wszeto9/ESP32-S3-HUB75-Driver/Firmware/007Gameboard/Gameboard_2025/ImageAssets.h

static char SwitchDisconnectedWhite[] = {
0x00, 0x00, 0x00, 0x00, 0x00, 0x00, 0x00, 0x00, 0x00, 0x00, 0x00, 0x00, 0x00, 0x00, 0x00, 0x00,
0x00, 0x00, 0x00, 0x00, 0x00, 0x00, 0x00, 0x00, 0x00, 0x00, 0x00, 0x00, 0x00, 0x00, 0x00, 0x00,
0x00, 0x0c, 0x00, 0x00, 0x00, 0x1e, 0x00, 0x00, 0xf8, 0xff, 0xff, 0x07, 0xf8, 0xff, 0xff, 0x07,
0xf8, 0xff, 0xff, 0x07, 0xf8, 0xff, 0xff, 0x07, 0xf8, 0xff, 0xff, 0x07, 0xf8, 0xff, 0xff, 0x07,
0xf8, 0xff, 0xff, 0x07, 0xf8, 0xff, 0xff, 0x07, 0xf8, 0xff, 0xff, 0x07, 0xf8, 0xff, 0xff, 0x07,
0x00, 0x00, 0x00, 0x00, 0x00, 0x00, 0x00, 0x00, 0x00, 0x00, 0x00, 0x00, 0x00, 0x00, 0x00, 0x00,
0x00, 0x00, 0x00, 0x00, 0x00, 0x00, 0x00, 0x00, 0x00, 0x00, 0x00, 0x00, 0x00, 0x00, 0x00, 0x00,
0x00, 0x00, 0x00, 0x00, 0x00, 0x00, 0x00, 0x00, 0x00, 0x00, 0x00, 0x00, 0x00, 0x00, 0x00, 0x00,
0x00, 0x00, 0x00, 0x00, 0x00, 0x00, 0x00, 0x00, 0x00, 0x00, 0x00, 0x00, 0x00, 0x00, 0x00, 0x00,
0x00, 0x00, 0x00, 0x00, 0x00, 0x00, 0x00, 0x00, 0x00, 0x00, 0x00, 0x00, 0x00, 0x00, 0x00, 0x00,
0x00, 0x00, 0x00, 0x00, 0x00, 0x00, 0x00, 0x00, 0x00, 0x00, 0x00, 0x00, 0x00, 0x00, 0x00, 0x00,
0x00, 0x00, 0x00, 0x00, 0x00, 0x00, 0x00, 0x00, 0x00, 0x00, 0x00, 0x00, 0x00, 0x00, 0x00, 0x00,
0x00, 0x00, 0x00, 0x00, 0x00, 0x00, 0x00, 0x00, 0x00, 0x00, 0x00, 0x00, 0x00, 0x00, 0x00, 0x00,
0xe0, 0xd2, 0x5d, 0x02, 0x20, 0x52, 0x44, 0x01, 0x20, 0xde, 0xc5, 0x00, 0x20, 0x52, 0x44, 0x01,
0xe0, 0xd2, 0x5d, 0x02, 0x00, 0x00, 0x00, 0x00, 0x9c, 0xa8, 0xef, 0x12, 0x84, 0x28, 0x22, 0x12,
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
0x00, 0x00, 0x00, 0x00, 0x00, 0x00, 0x00, 0x00, 0x00, 0x00, 0x00, 0x00, 0x00, 0x00, 0x00, 0x00,
0x00, 0x00, 0x00, 0x00, 0x00, 0x00, 0x00, 0x00, 0x00, 0x00, 0x00, 0x00, 0x00, 0x00, 0x00, 0x00,
0x00, 0x00, 0x00, 0x00, 0x00, 0x00, 0x00, 0x00, 0x00, 0x00, 0x00, 0x00, 0x00, 0x00, 0x00, 0x00
};
