wszeto9/ESP32-S3-HUB75-Driver/Firmware/007Gameboard/Gameboard_Spaceship/VisualAssets.h

const char NoAccelWhite[] PROGMEM =  {
0x00, 0x00, 0x00, 0x00, 0x00, 0x00, 0x00, 0x00, 0xf8, 0xff, 0xff, 0x1f, 0x00, 0x00, 0x00, 0x00,
0x0c, 0x00, 0x00, 0x30, 0xe0, 0xd2, 0x5d, 0x02, 0x06, 0x80, 0x01, 0x60, 0x20, 0x52, 0x44, 0x01,
0x02, 0xc0, 0x03, 0x40, 0x20, 0xde, 0xc5, 0x00, 0x02, 0xe0, 0x07, 0x40, 0x20, 0x52, 0x44, 0x01,
0x02, 0xf0, 0x0f, 0x40, 0xe0, 0xd2, 0x5d, 0x02, 0x02, 0x80, 0x01, 0x40, 0x00, 0x00, 0x00, 0x00,
0x02, 0x80, 0x01, 0x40, 0x00, 0x00, 0x00, 0x00, 0x02, 0x80, 0x01, 0x40, 0x00, 0x00, 0x00, 0x00,
0x02, 0x80, 0x01, 0x40, 0x70, 0xe9, 0x95, 0x0e, 0x02, 0xe0, 0x07, 0x40, 0x10, 0x2b, 0xb4, 0x02,
0x42, 0x10, 0x08, 0x40, 0x70, 0xaf, 0xf5, 0x0e, 0x62, 0x08, 0x10, 0x40, 0x10, 0x2d, 0xd5, 0x02,
0x72, 0xc8, 0x13, 0x40, 0x70, 0xe9, 0x95, 0x0e, 0xfa, 0xcf, 0x13, 0x40, 0x00, 0x00, 0x00, 0x00,
0xfa, 0xcf, 0x13, 0x40, 0x00, 0x00, 0x00, 0x00, 0x72, 0xc8, 0x13, 0x40, 0x00, 0x00, 0x00, 0x00,
0x62, 0x08, 0x10, 0x40, 0x00, 0x00, 0x00, 0x00, 0x42, 0x10, 0x18, 0x40, 0x00, 0x00, 0x00, 0x00,
0x02, 0xe0, 0x3f, 0x40, 0x00, 0x00, 0x00, 0x00, 0x02, 0x00, 0x70, 0x44, 0x00, 0x00, 0x00, 0x00,
0x02, 0x00, 0xe0, 0x46, 0x00, 0x00, 0x00, 0x00, 0x02, 0x00, 0xc0, 0x47, 0x00, 0x00, 0x00, 0x00,
0x02, 0x00, 0x80, 0x47, 0x00, 0x00, 0x00, 0x00, 0x02, 0x00, 0xc0, 0x47, 0x00, 0x00, 0x00, 0x00,
0x02, 0x00, 0xe0, 0x47, 0x00, 0x00, 0x00, 0x00, 0x02, 0x00, 0x00, 0x40, 0x00, 0x00, 0x00, 0x00,
0x06, 0x00, 0x00, 0x60, 0x00, 0x00, 0x00, 0x00, 0x0c, 0x00, 0x00, 0x30, 0x00, 0x00, 0x00, 0x00,
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
0x70, 0x00, 0x00, 0x0e, 0x70, 0xf7, 0xae, 0x0e, 0x38, 0x00, 0x00, 0x1c, 0x40, 0xd1, 0xa8, 0x06,
0x1c, 0x00, 0x00, 0x38, 0x70, 0x97, 0xee, 0x0a, 0x0e, 0x00, 0x00, 0x70, 0x00, 0x00, 0x00, 0x00,
0x07, 0x00, 0x00, 0xe0, 0x00, 0x00, 0x00, 0x00, 0x03, 0x00, 0x00, 0xc0, 0x00, 0x00, 0x00, 0x00
};
