wszeto9/ESP32-S3-HUB75-Driver/Firmware/ESP32S3_Firmware/logos.h

const char MBTA_bits[] PROGMEM= {
0x1c, 0x22, 0x5d, 0x49, 0x49, 0x22, 0x1c
};

const char MIT_bits[] PROGMEM= {
0x00, 0x00, 0x55, 0x07, 0x15, 0x00, 0x55, 0x01, 0x51, 0x01, 0x51, 0x01, 0x00, 0x00
};

const char bus_bits[] PROGMEM = {
  0x1e, 0x21, 0x21, 0x3f, 0x2d, 0x3f, 0x12
};

const char walk_bits[] PROGMEM = {
  0x18, 0x18, 0x0e, 0x38, 0x08, 0x14, 0x12
};

const char clock_circle_bits[] PROGMEM = {
  0x1c, 0x22, 0x41, 0x41, 0x41, 0x22, 0x1c
};

const char clock_hands_bits[] PROGMEM = {
  0x00, 0x08, 0x08, 0x38, 0x00, 0x00, 0x00
};
